Project-Lily/wonder-model/images/v2inside.jpg

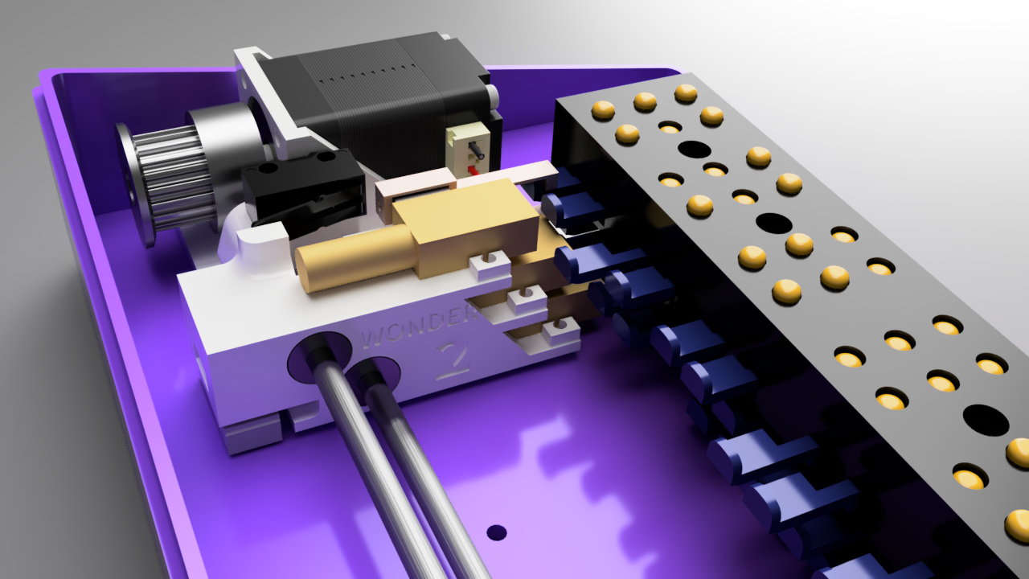
images/v2inside.jpg
