Project-Lily/wonder-model/images/Wonder_Reader_2_2023-May-07_06-18-13AM-000_CustomizedView25365315556_png.png

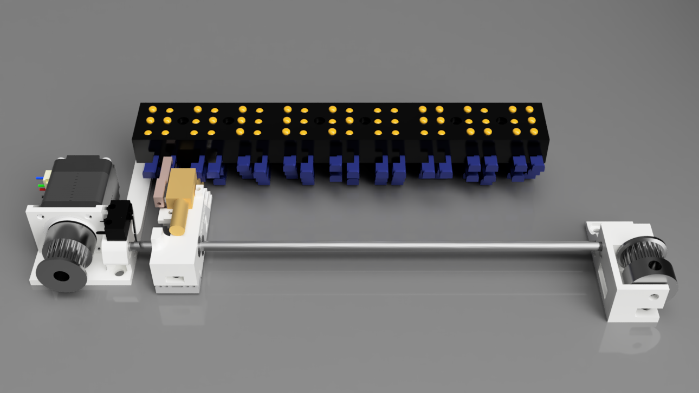
images/Wonder_Reader_2_2023-May-07_06-18-13AM-000_CustomizedView25365315556_png.png
