Project-Lily/wonder-model/images/Wonder_Reader_2_2023-May-07_06-40-11AM-000_CustomizedView41625912806_png.png

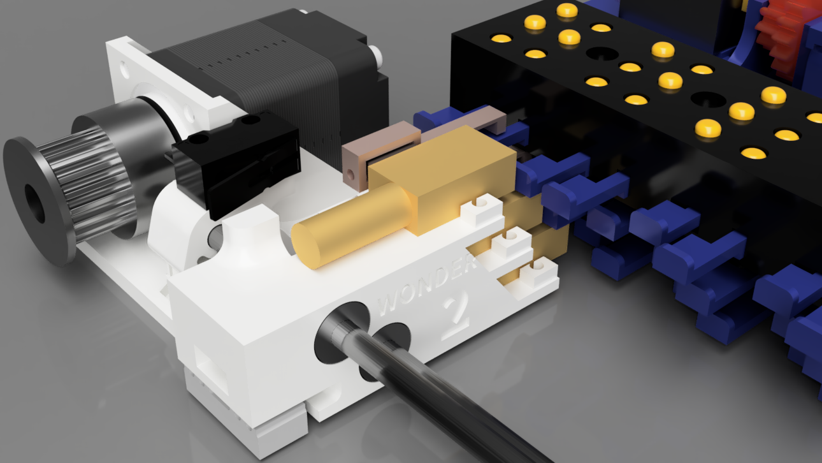
images/Wonder_Reader_2_2023-May-07_06-40-11AM-000_CustomizedView41625912806_png.png
