Project-Lily/wonder-model/images/wonder_reader_pusher_WIP.png

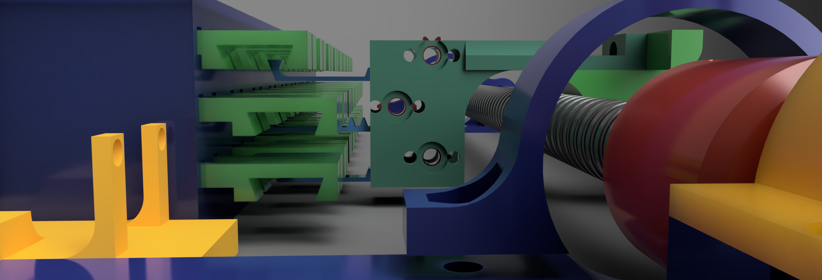
images/wonder_reader_pusher_WIP.png
