Project-Lily/wonder-model/prototype/Mk2/keycap1.25.stl

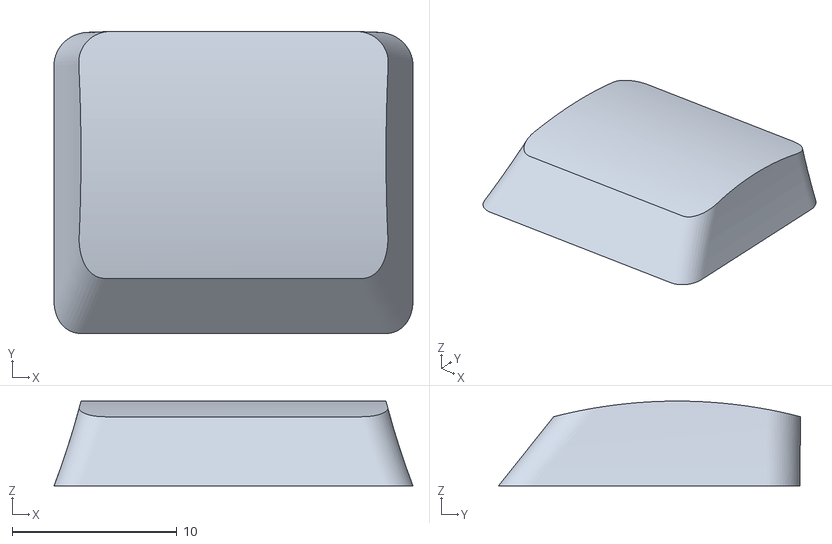
[picture p34: CAD file, 2023-06-01]
prototype/Mk2/keycap1.25.stl
21.8 x 18.3 x 5.15
