Project-Lily/wonder-model/prototype/Mk2/keycapbump.stl

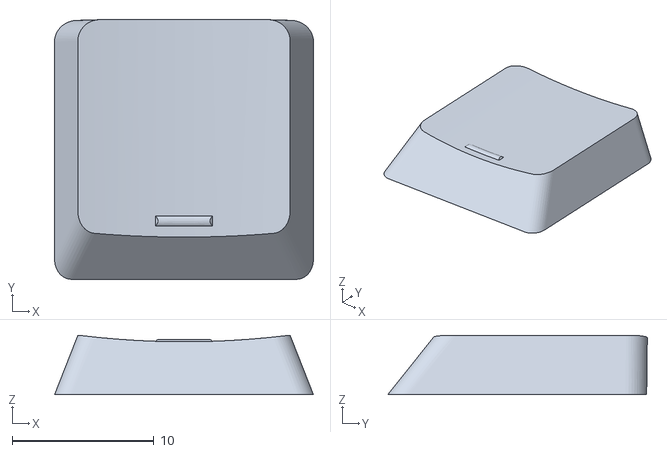
[picture p35: CAD file, 2023-06-01]
prototype/Mk2/keycapbump.stl
18.3 x 18.3 x 4.20
