Project-Lily/wonder-model/prototype/Mk2/top-2.stl

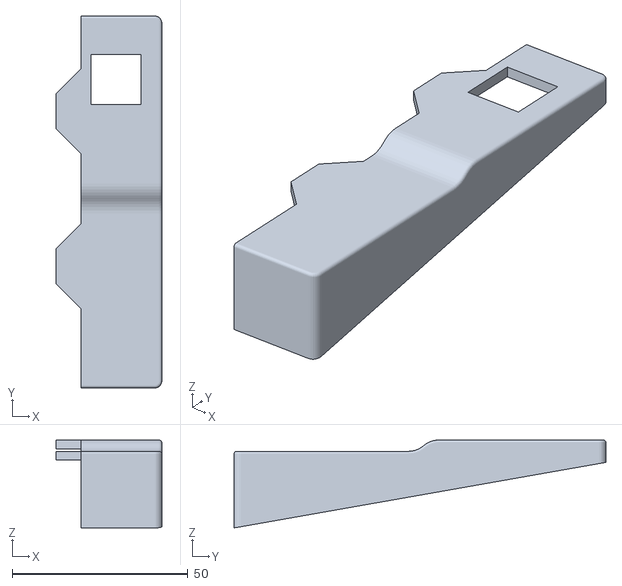
[picture p36: CAD file, 2023-06-01]
prototype/Mk2/top-2.stl
30.1 x 105.8 x 25.0
