Project-Lily/wonder-model/prototype/Mk2/holder-left.stl

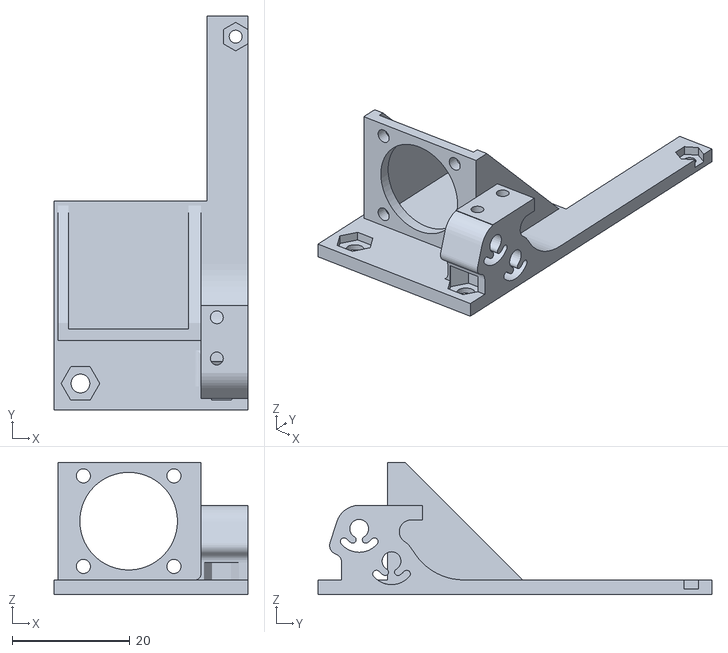
[picture p37: CAD file, 2023-06-01]
prototype/Mk2/holder-left.stl
33.0 x 67.0 x 22.5
