Project-Lily/wonder-model/prototype/Mk2/wedge6.stl

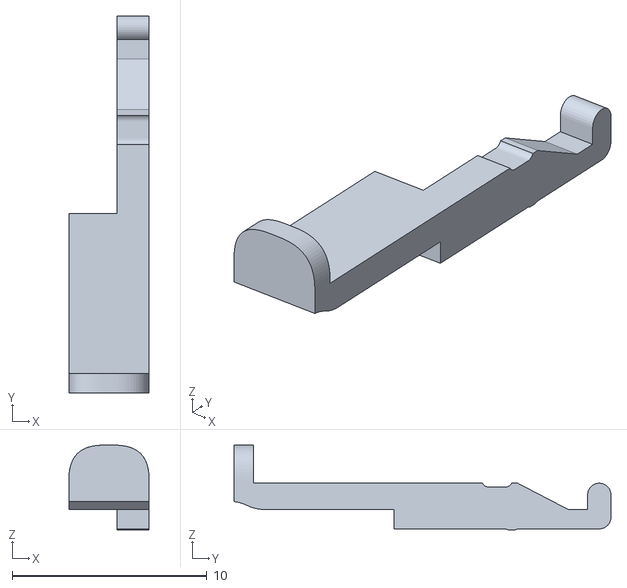
[picture p38: CAD file, 2023-06-01]
prototype/Mk2/wedge6.stl
4.13 x 19.3 x 4.35
