Project-Lily/wonder-model/prototype/Mk2/keycap1uspeaker.stl

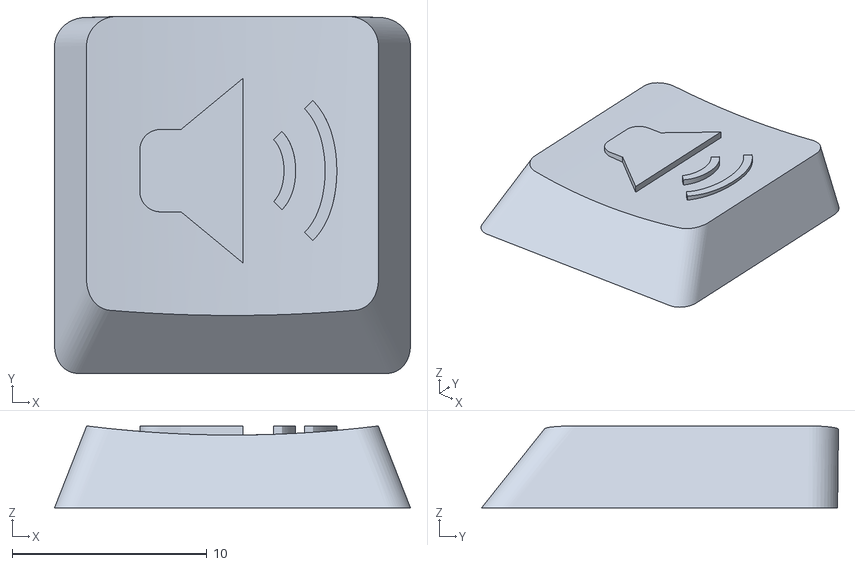
[picture p39: CAD file, 2023-06-01]
prototype/Mk2/keycap1uspeaker.stl
18.3 x 18.3 x 4.20
