Project-Lily/wonder-model/prototype/Mk2/cell_body.stl

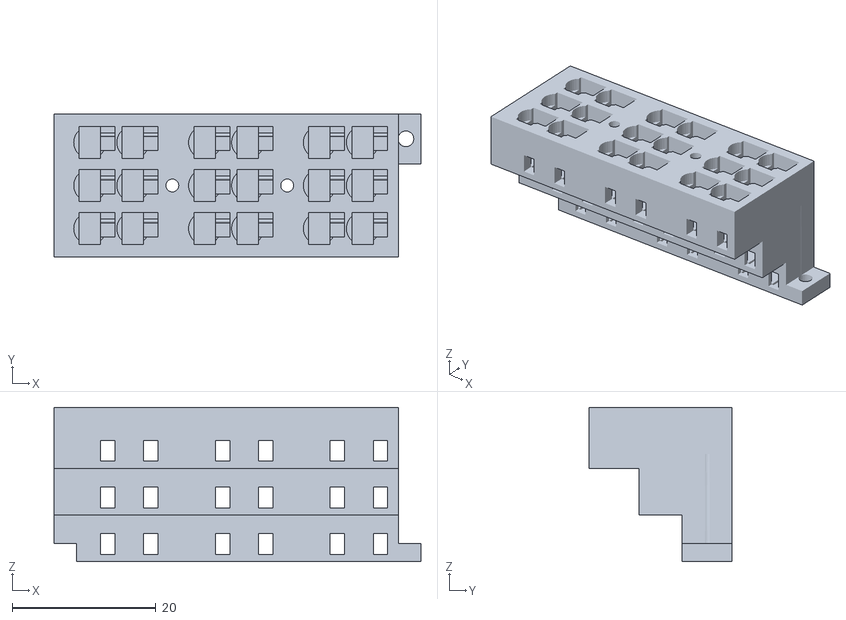
[picture p40: CAD file, 2023-06-01]
prototype/Mk2/cell_body.stl
51.2 x 20.0 x 21.5
