Project-Lily/wonder-model/prototype/Mk2/badge.stl

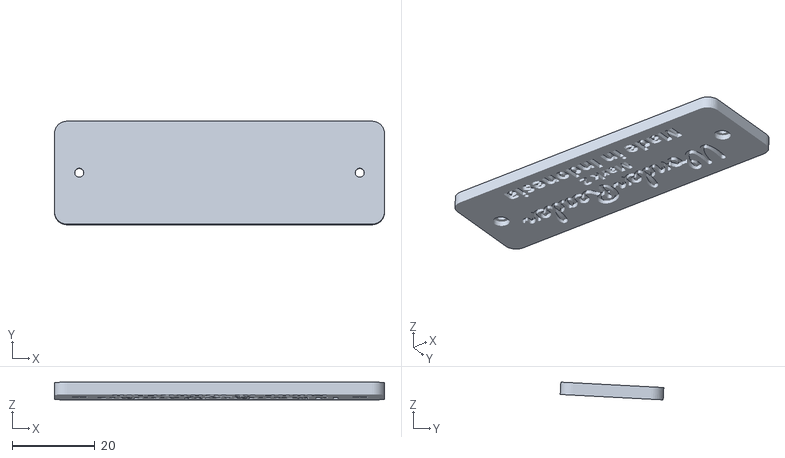
[picture p41: CAD file, 2023-06-01]
prototype/Mk2/badge.stl
80.0 x 25.1 x 4.30
