Project-Lily/wonder-model/prototype/Mk2/carriage.stl

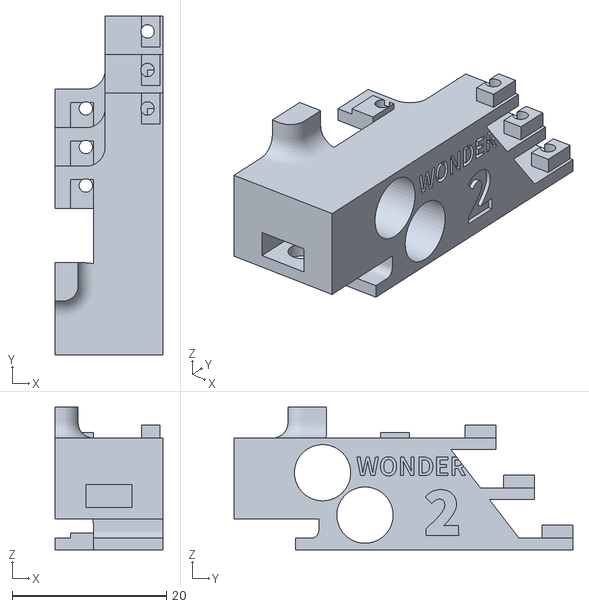
[picture p42: CAD file, 2023-06-01]
prototype/Mk2/carriage.stl
14.0 x 44.0 x 18.5
