Project-Lily/wonder-model/prototype/Mk2/clamp.stl

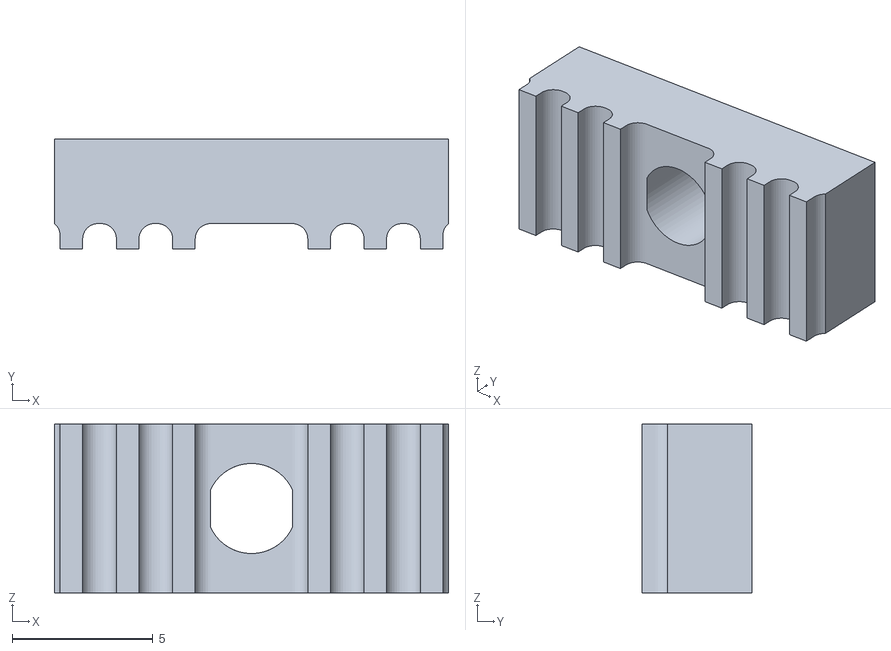
[picture p43: CAD file, 2023-06-01]
prototype/Mk2/clamp.stl
14.0 x 3.90 x 6.00
