Project-Lily/wonder-model/prototype/Mk2/top-1.stl

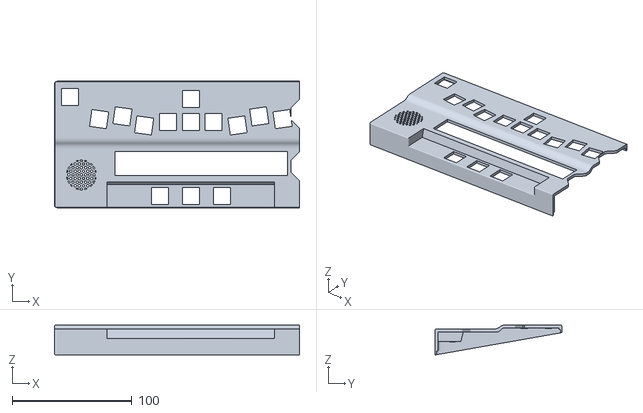
[picture p44: CAD file, 2023-06-01]
prototype/Mk2/top-1.stl
204.9 x 105.8 x 25.0
