Project-Lily/wonder-model/prototype/Mk2/single_top.stl

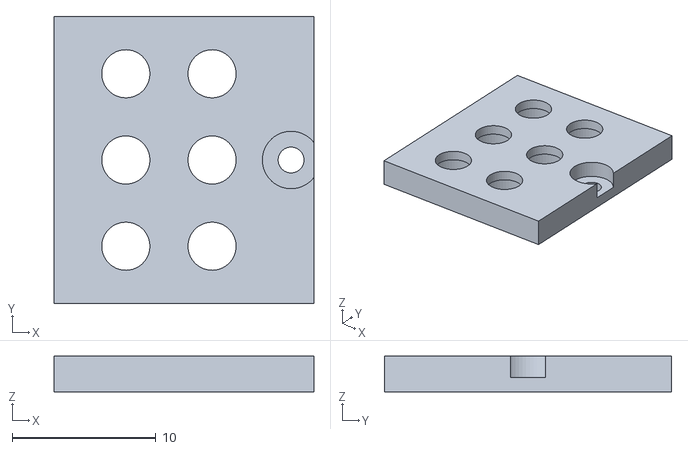
[picture p45: CAD file, 2023-06-01]
prototype/Mk2/single_top.stl
18.1 x 20.0 x 2.50
