Project-Lily/wonder-model/prototype/Mk2/single_top_half.stl

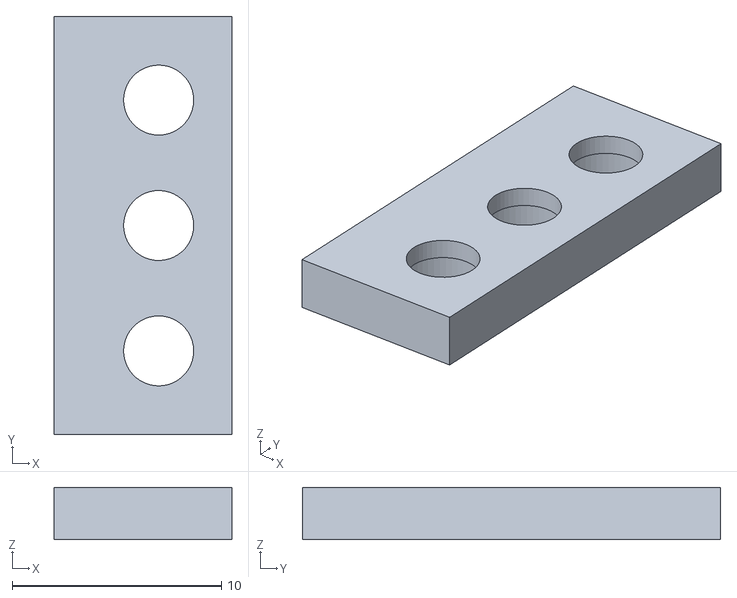
[picture p46: CAD file, 2023-06-01]
prototype/Mk2/single_top_half.stl
8.50 x 20.0 x 2.50
