Project-Lily/wonder-model/prototype/Mk2/cell_top.stl

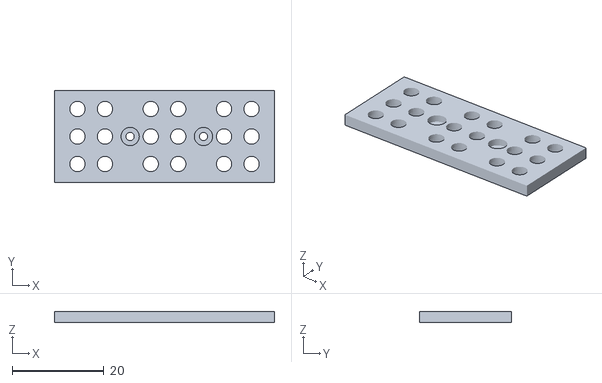
[picture p47: CAD file, 2023-06-01]
prototype/Mk2/cell_top.stl
48.0 x 20.0 x 2.50
