Project-Lily/wonder-model/prototype/Mk2/single_body.stl

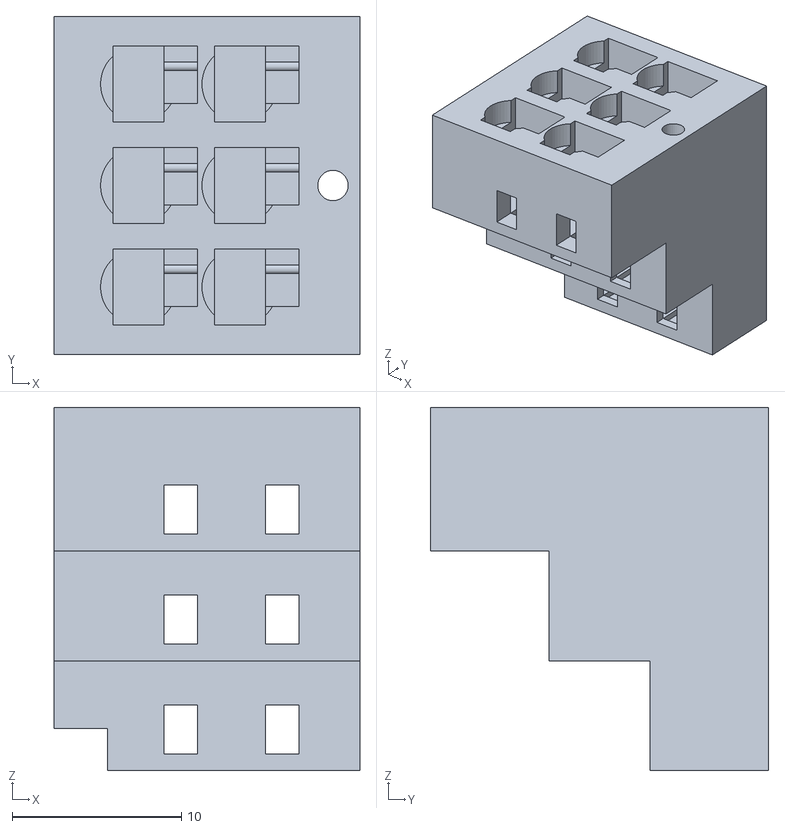
[picture p48: CAD file, 2023-06-01]
prototype/Mk2/single_body.stl
18.1 x 20.0 x 21.5
