Project-Lily/wonder-model/prototype/Mk2/keycaplong1.75u.stl

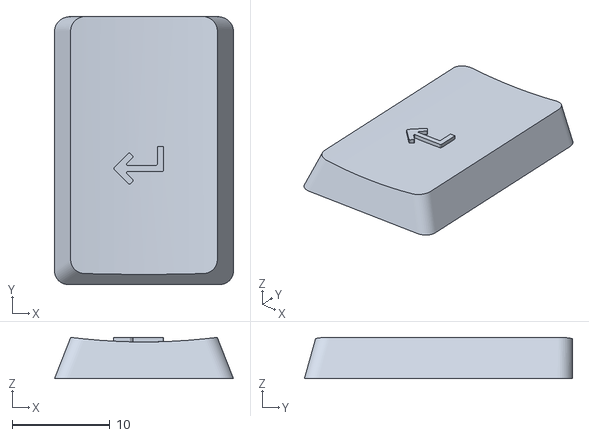
[picture p49: CAD file, 2023-06-01]
prototype/Mk2/keycaplong1.75u.stl
18.3 x 27.4 x 4.20
