Project-Lily/wonder-model/prototype/Mk2/single_body_half.stl

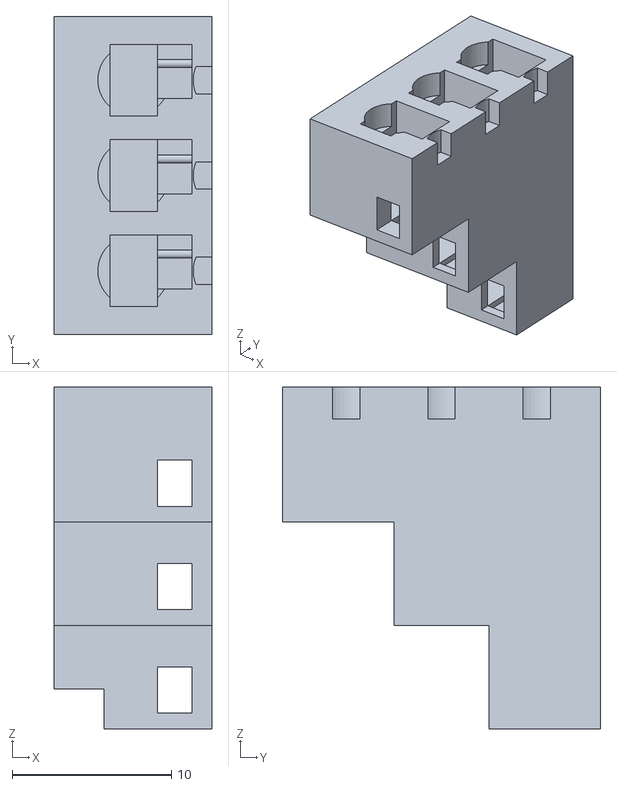
[picture p50: CAD file, 2023-06-01]
prototype/Mk2/single_body_half.stl
9.92 x 20.0 x 21.5
