Project-Lily/wonder-model/prototype/Mk2/keycap1.75.stl

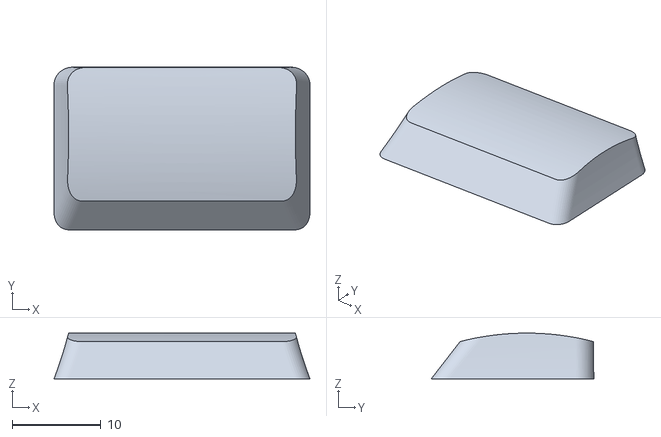
[picture p51: CAD file, 2023-06-01]
prototype/Mk2/keycap1.75.stl
28.8 x 18.3 x 5.15
