Project-Lily/wonder-model/prototype/Mk2/pin2.stl

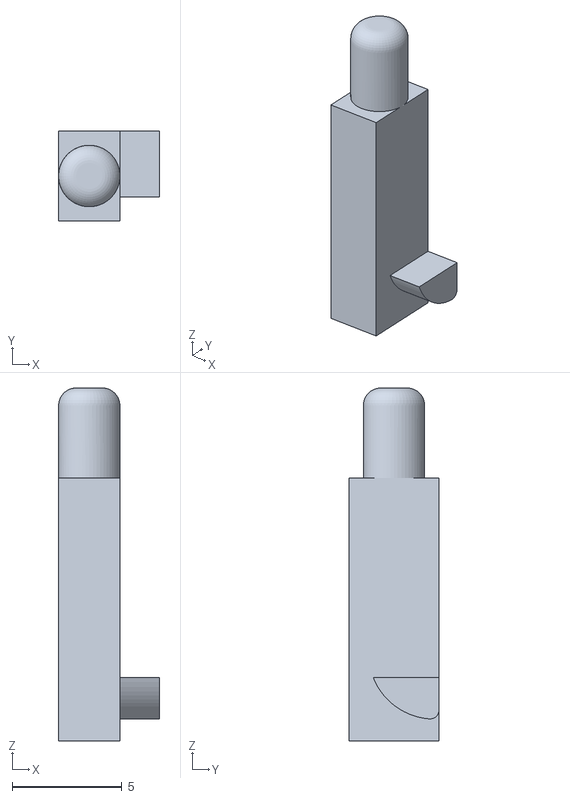
[picture p52: CAD file, 2023-05-15]
prototype/Mk2/pin2.stl
4.60 x 4.10 x 16.1
