Project-Lily/wonder-model/prototype/Mk2/pin1.stl

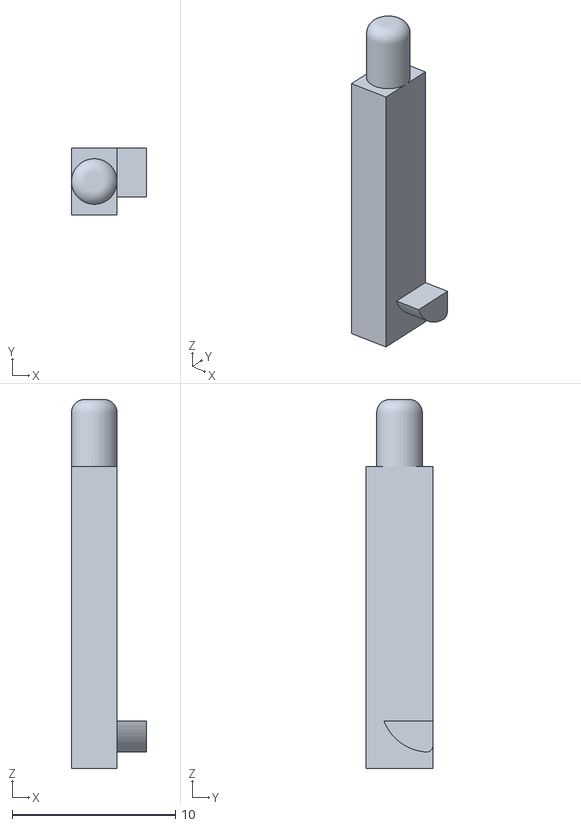
[picture p53: CAD file, 2023-05-15]
prototype/Mk2/pin1.stl
4.60 x 4.10 x 22.6
