Project-Lily/wonder-model/prototype/Mk2/pin3.stl

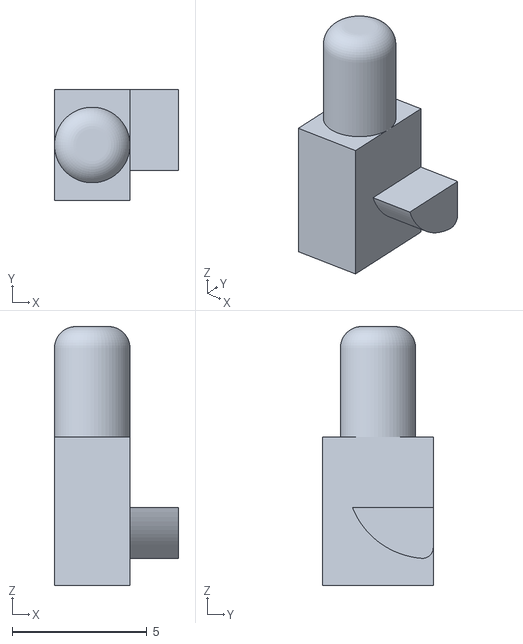
[picture p54: CAD file, 2023-05-15]
prototype/Mk2/pin3.stl
4.60 x 4.10 x 9.60
