Project-Lily/wonder-model/prototype/Mk2/wedge_clearer.stl

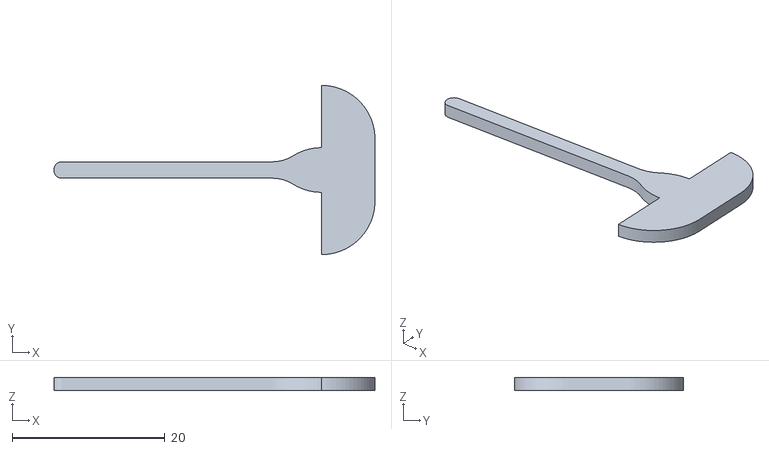
[picture p55: CAD file, 2023-05-15]
prototype/Mk2/wedge_clearer.stl
42.0 x 22.2 x 1.65
